Fire-Devils/FilaMan-System-ESP32/src/wlan.h

#ifndef WLAN_H
#define WLAN_H

#include <Arduino.h>

void initWiFi();
void checkWiFiConnection();

// Sendeleistung in 0.1 dBm (85/110/130/150/170/195). Ungueltige Werte werden ignoriert.
bool isValidTxPowerDeciDbm(int16_t deciDbm);
void loadWifiTxPower();
void saveWifiTxPower(int16_t deciDbm);

#endif
